VedanshMannem/LORA/photos/Screenshot 2025-11-28 172649.png

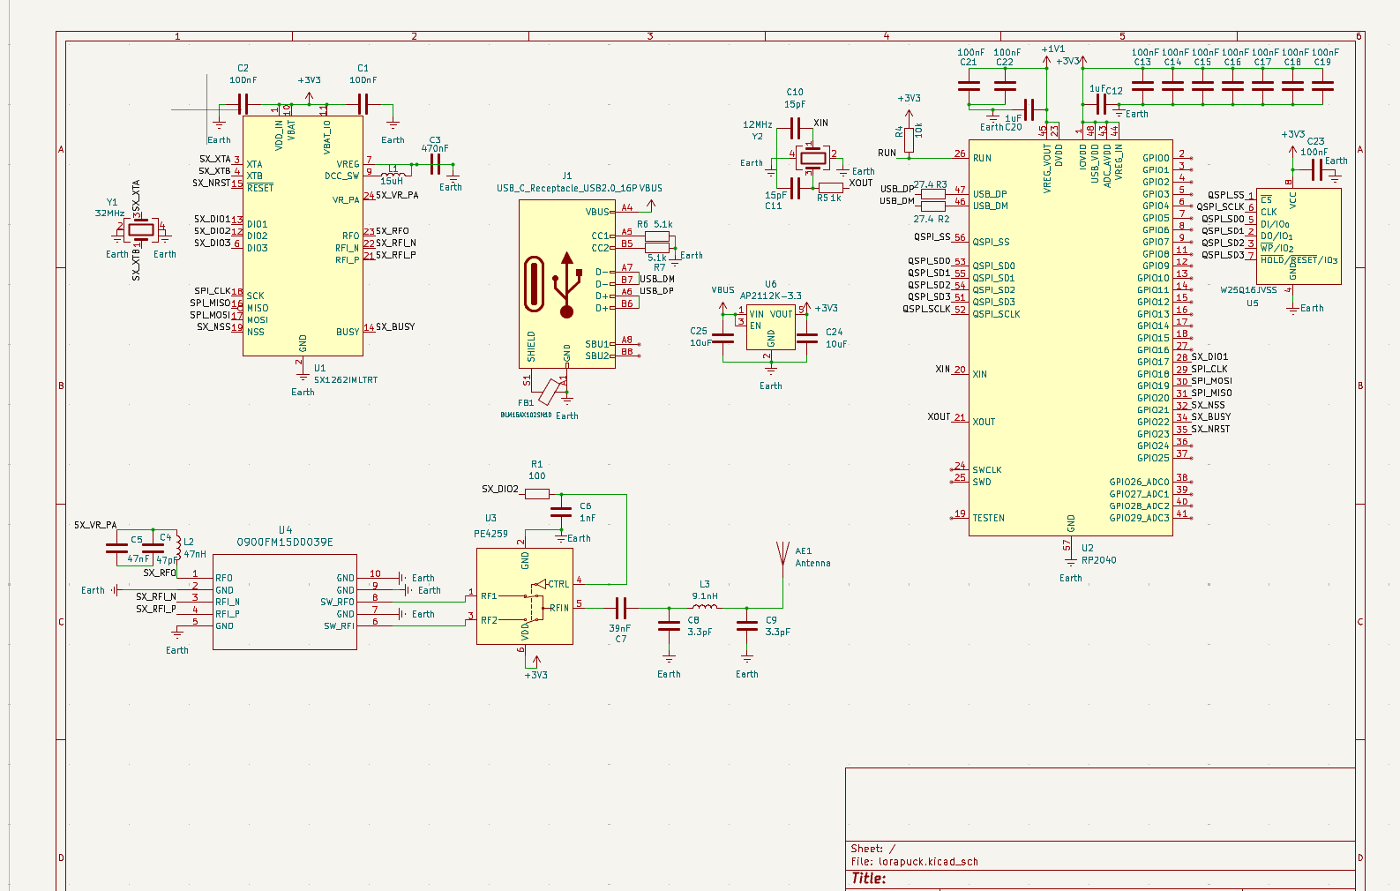
photos/Screenshot 2025-11-28 172649.png
