VedanshMannem/LORA/photos/Screenshot 2025-11-29 154143.png

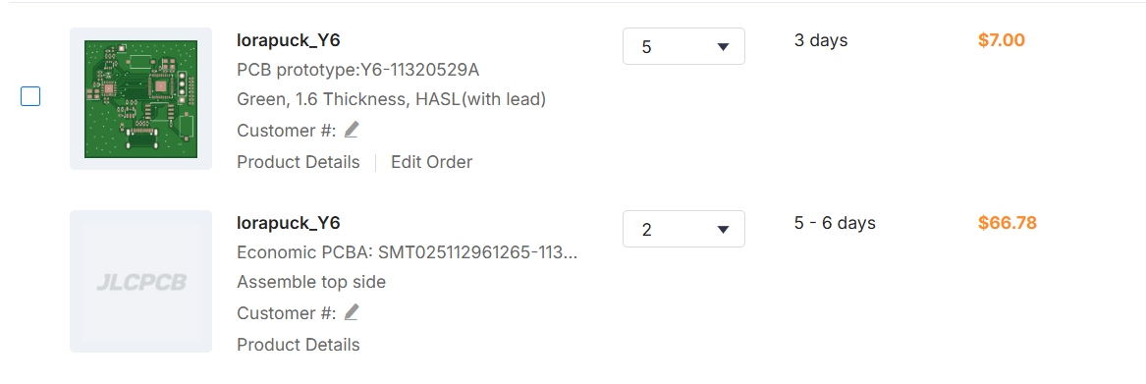
photos/Screenshot 2025-11-29 154143.png
