VedanshMannem/LORA/photos/Screenshot 2025-11-30 131133.png

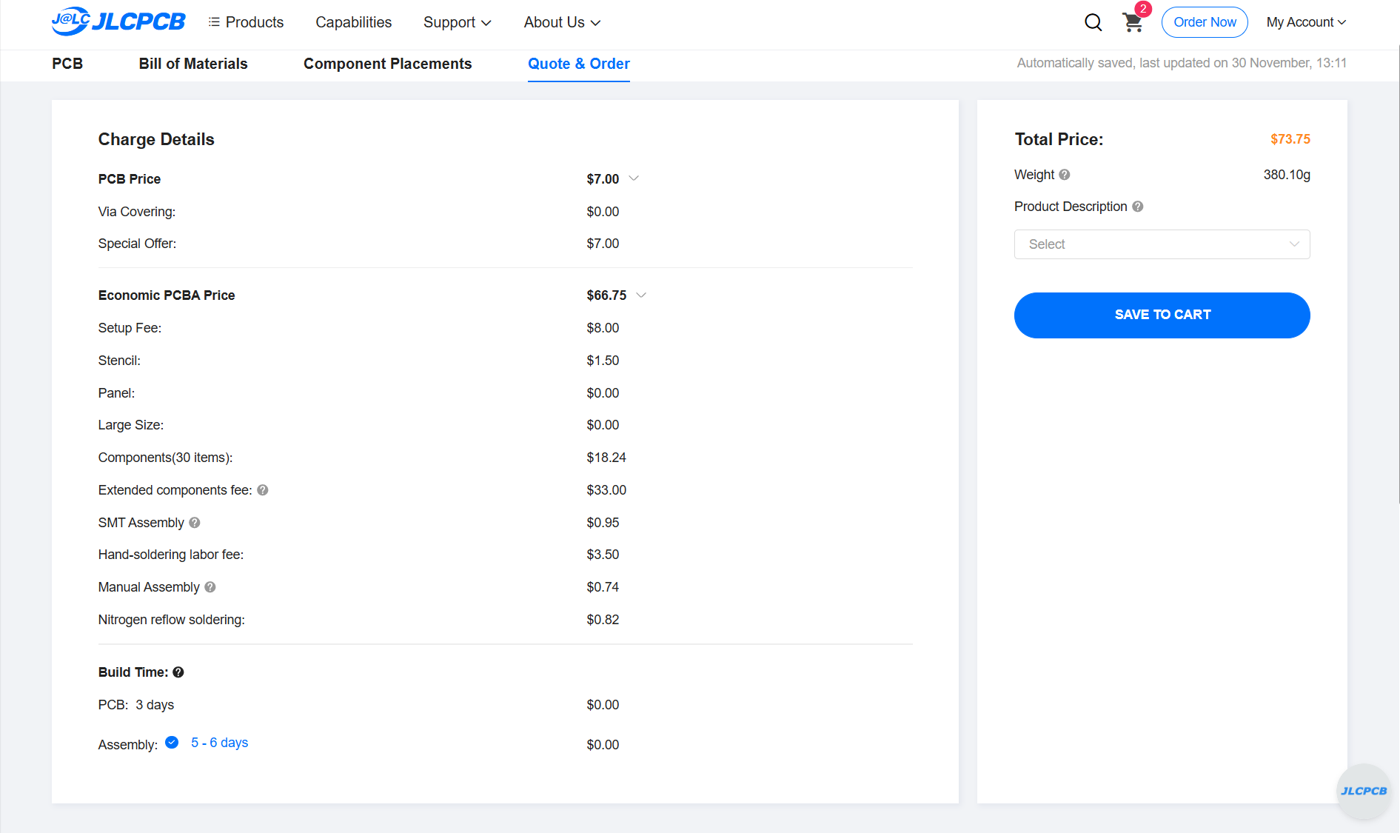
photos/Screenshot 2025-11-30 131133.png
